AP-IT-GH/jp19-luwb/src/AP lokalisatie/Anchors/Case/Afmetingen.jpg

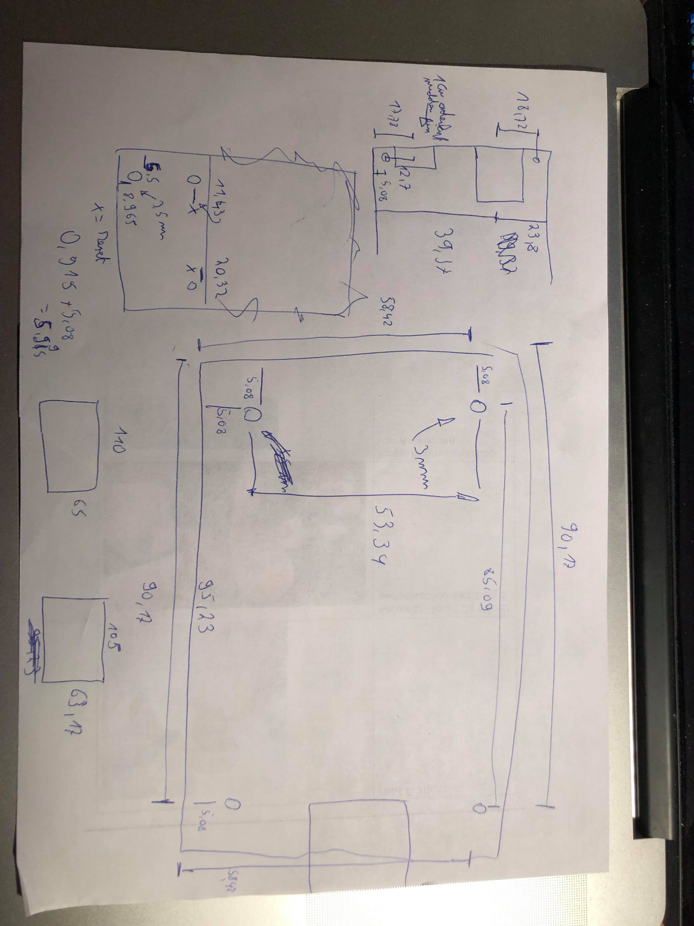
src/AP lokalisatie/Anchors/Case/Afmetingen.jpg
