AP-IT-GH/jp19-luwb/src/AP lokalisatie/Anchors/Case/Boxes.py instellingen.png

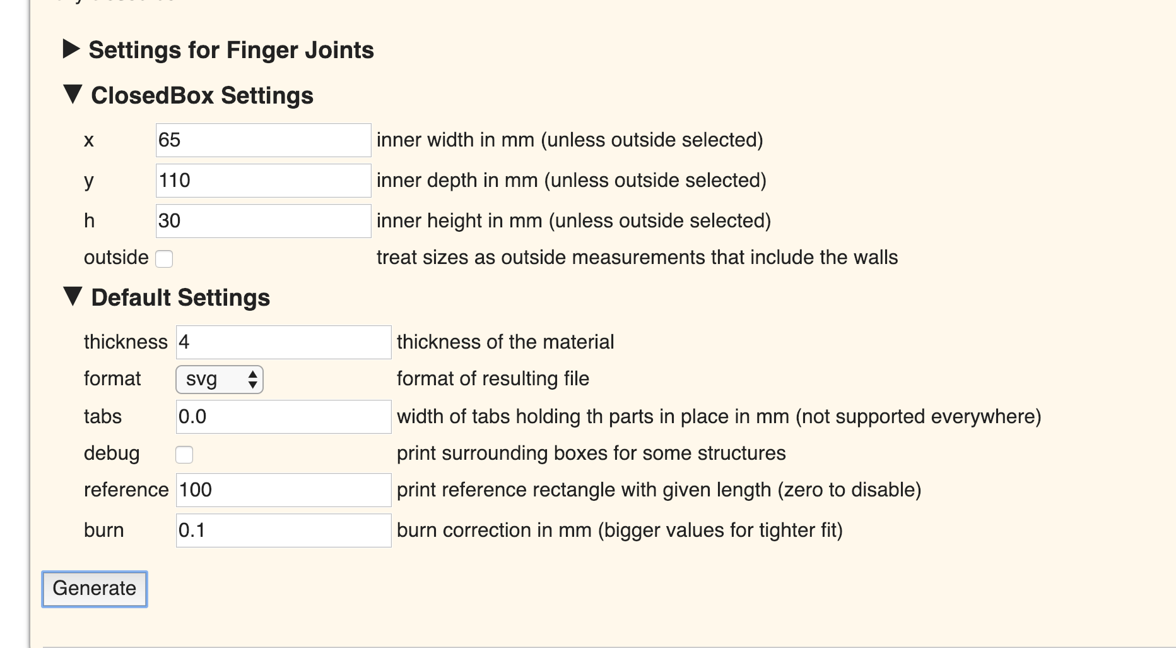
src/AP lokalisatie/Anchors/Case/Boxes.py instellingen.png
