AP-IT-GH/jp19-luwb/src/visualisatie/WebAppLUWB/src/assets/img/PageNotFoundPicture.png

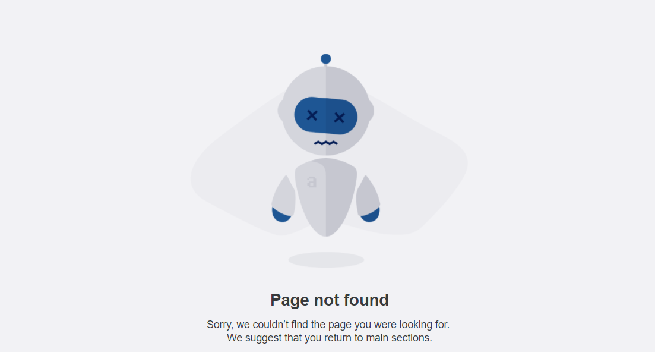
src/visualisatie/WebAppLUWB/src/assets/img/PageNotFoundPicture.png
