AP-IT-GH/jp19-luwb/src/visualisatie/WebAppLUWB/src/assets/img/POZYX.png

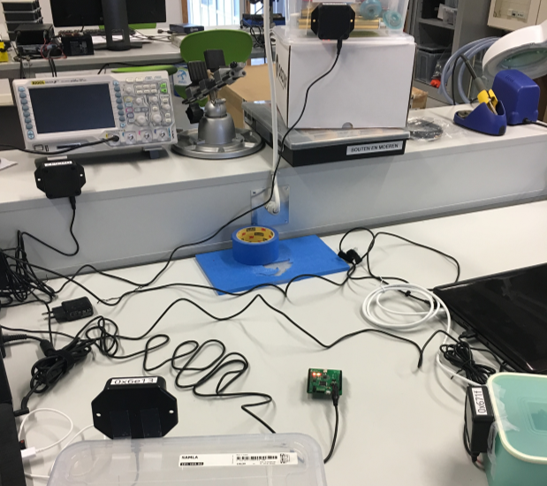
src/visualisatie/WebAppLUWB/src/assets/img/POZYX.png
