AP-IT-GH/jp19-luwb/src/visualisatie/WebAppLUWB/src/assets/img/uwb.png

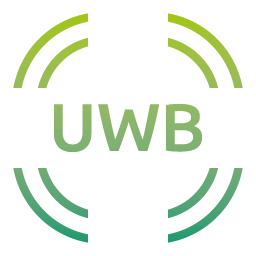
src/visualisatie/WebAppLUWB/src/assets/img/uwb.png
